EA11R/Suzuki-42P-ECU/Datasheet/IMG_0481.JPG

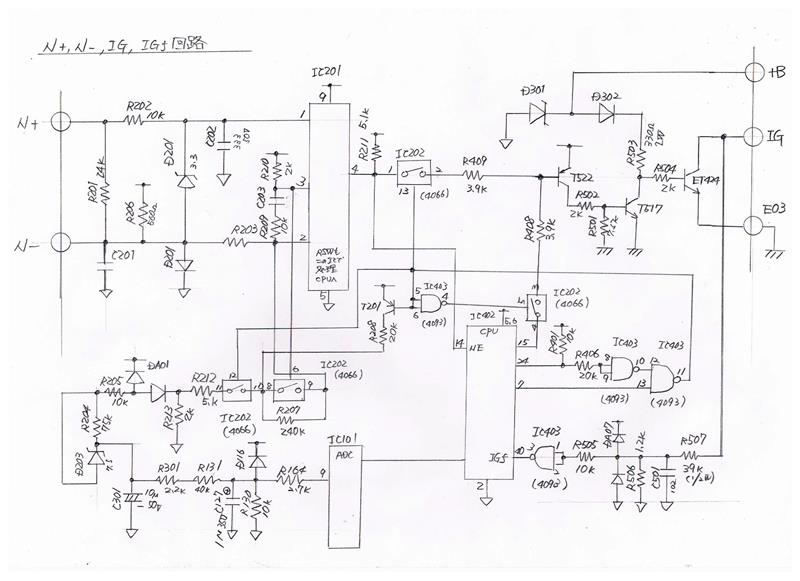
Datasheet/IMG_0481.JPG
