EA11R/Suzuki-42P-ECU/Datasheet/IMG_0482.JPG

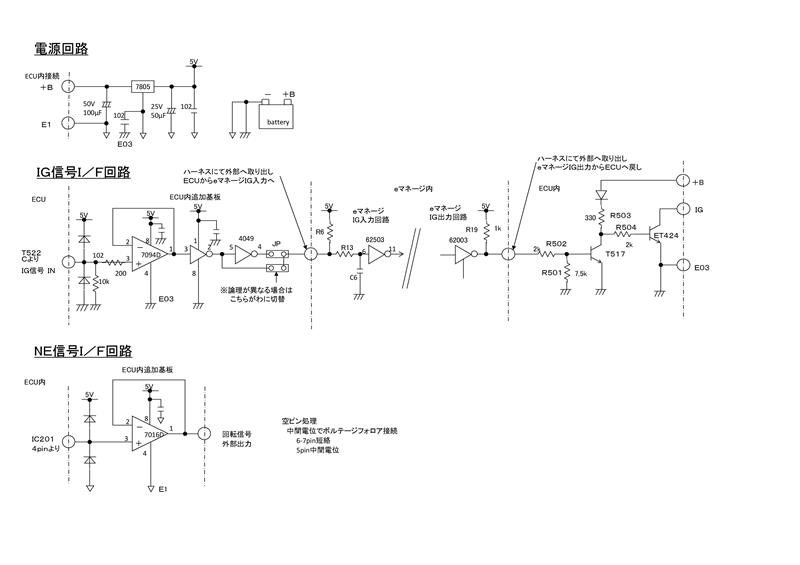
Datasheet/IMG_0482.JPG
