EA11R/Suzuki-42P-ECU/Datasheet/IMG_0484.JPG

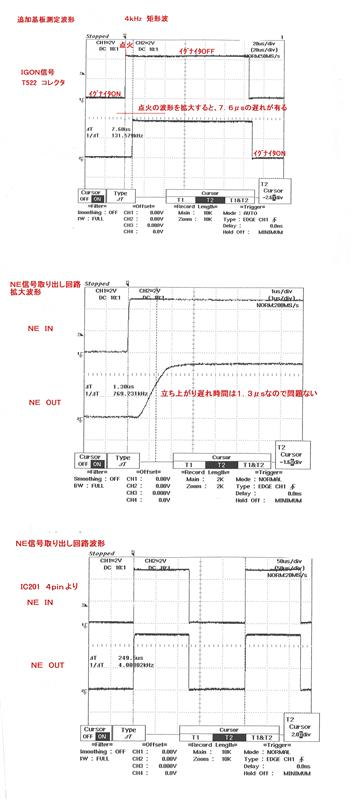
Datasheet/IMG_0484.JPG
