EA11R/Suzuki-42P-ECU/Datasheet/IMG_0489.JPG

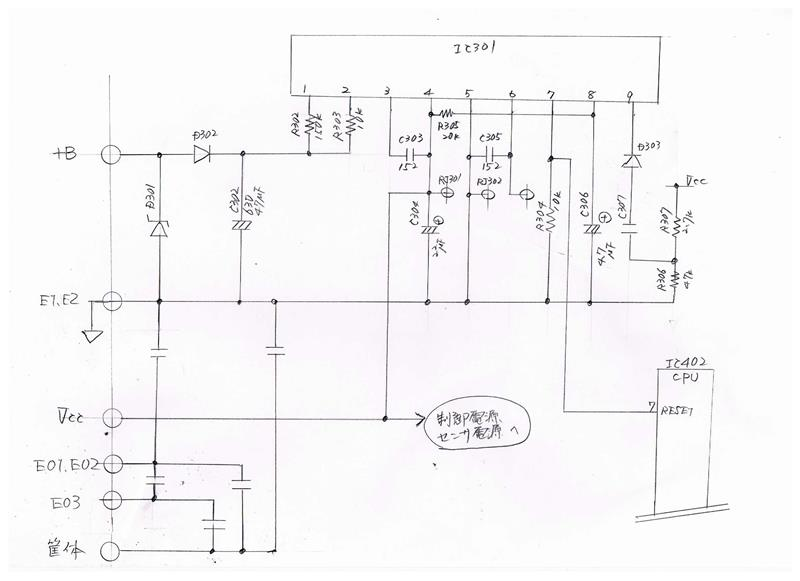
Datasheet/IMG_0489.JPG
