EA11R/Suzuki-42P-ECU/Datasheet/IMG_0493.JPG

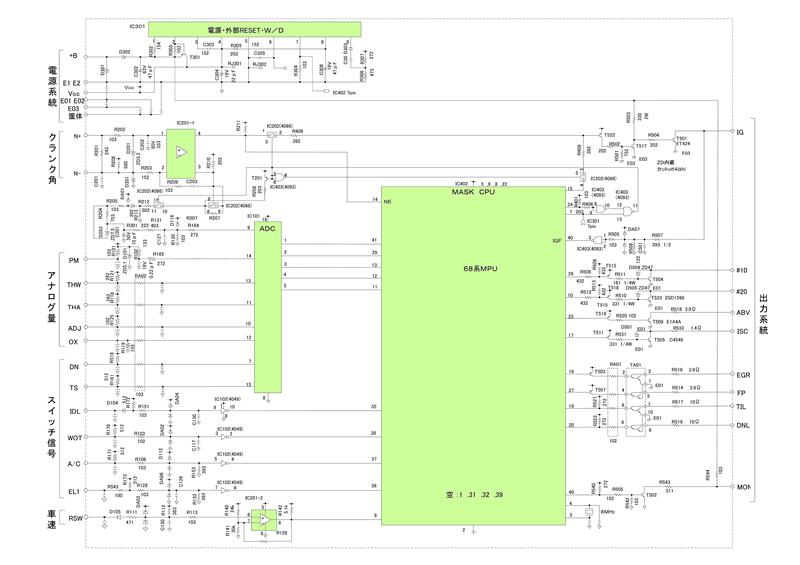
Datasheet/IMG_0493.JPG
