EA11R/Suzuki-42P-ECU/HKS_F_CONV_&_IS/F-con wiring.png

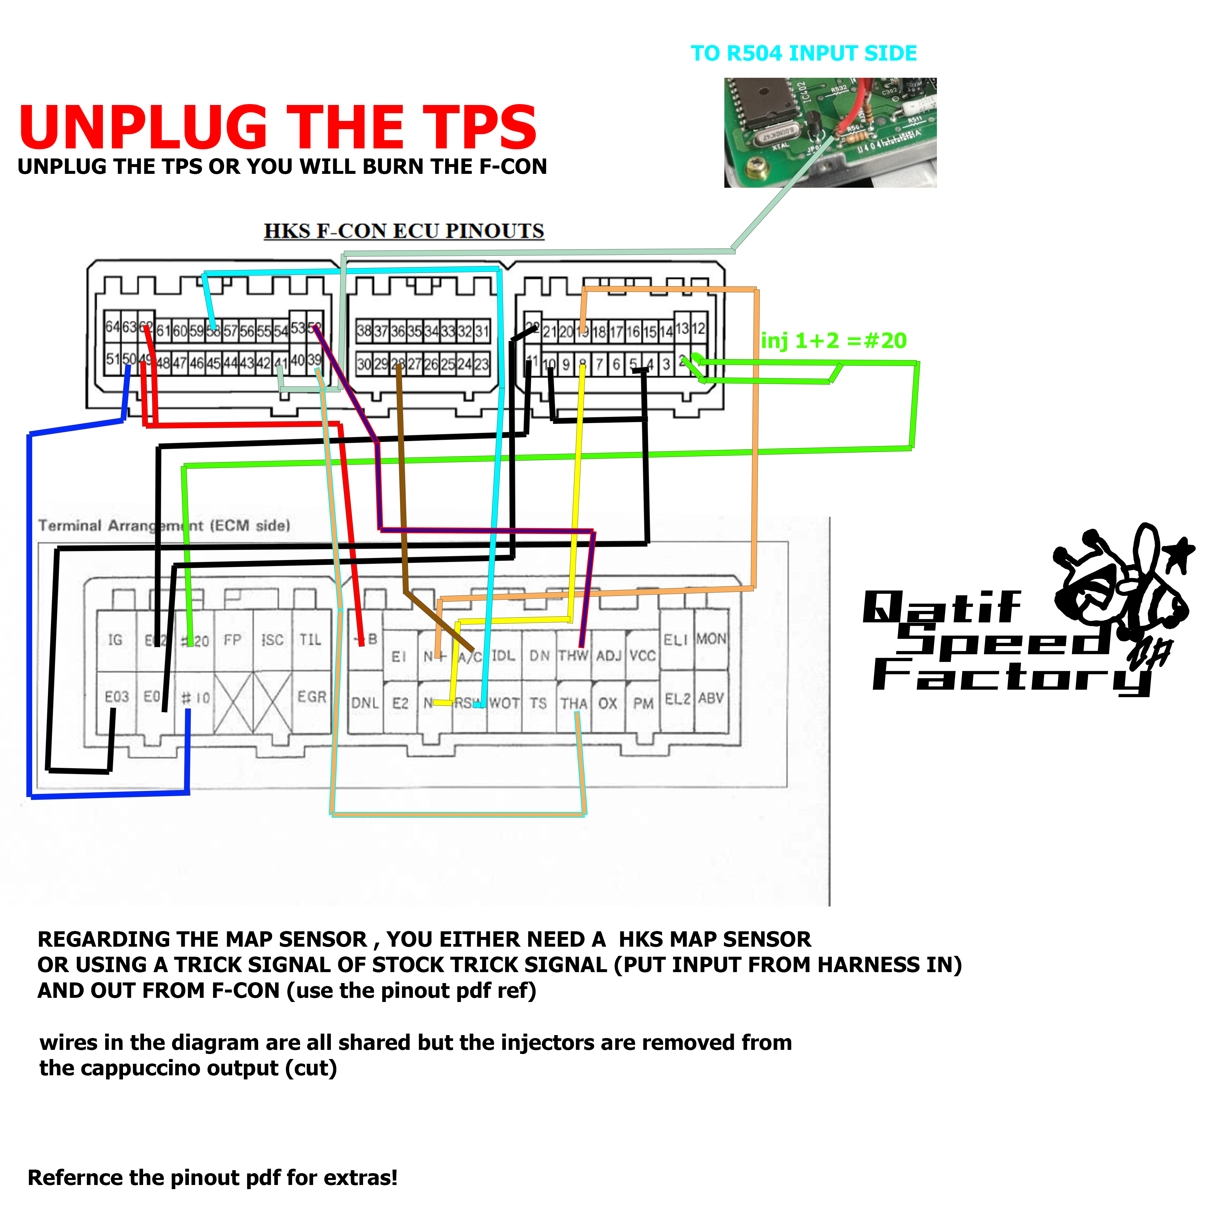
HKS_F_CONV_&_IS/F-con wiring.png
